rsna6ce/OLIXIE/fonts/image2cpp_settings.png

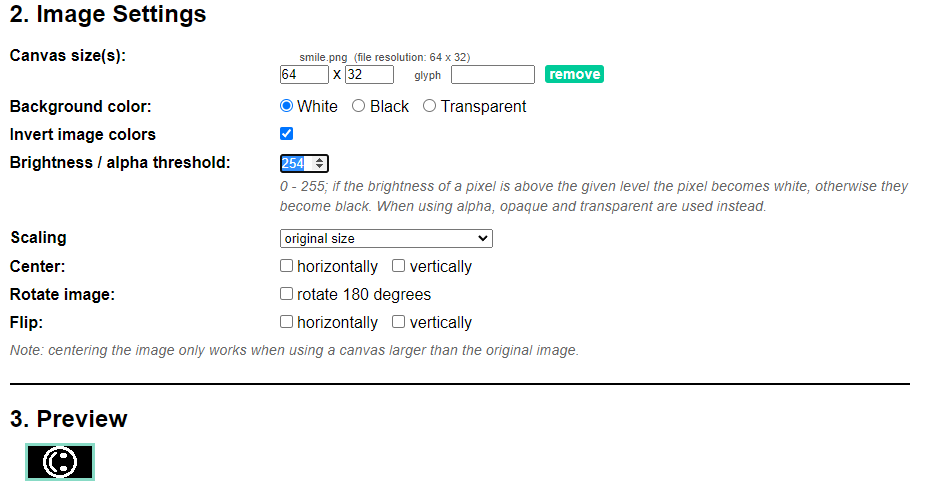
fonts/image2cpp_settings.png
